sTeeLM/FMTransmitor/Src/debug.h

#ifndef __FM_TRANS_DEBUG_H__
#define __FM_TRANS_DEBUG_H__

#include <stdio.h>

void debug_onoff(bit enable);
void debug_initialize(void);


#ifdef __FM_TRANS_DEBUG__
void debug_printf(const char * fmt, ...);
#define CDBG debug_printf
#else
#define CDBG
#endif

void debug_printf(const char * fmt, ...);

//#define CDBG debug_printf

#endif
